AntoineAndre/alpha_dre/docs/renders/alpha_dre_top_view2.png

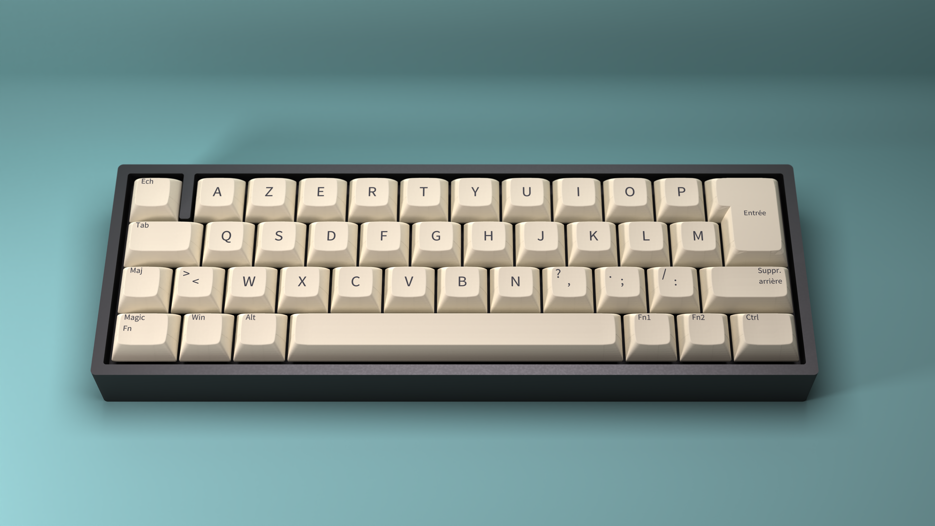
docs/renders/alpha_dre_top_view2.png
