AntoineAndre/alpha_dre/case/Rev2/solidworks_project/switch_plate.SLDPRT

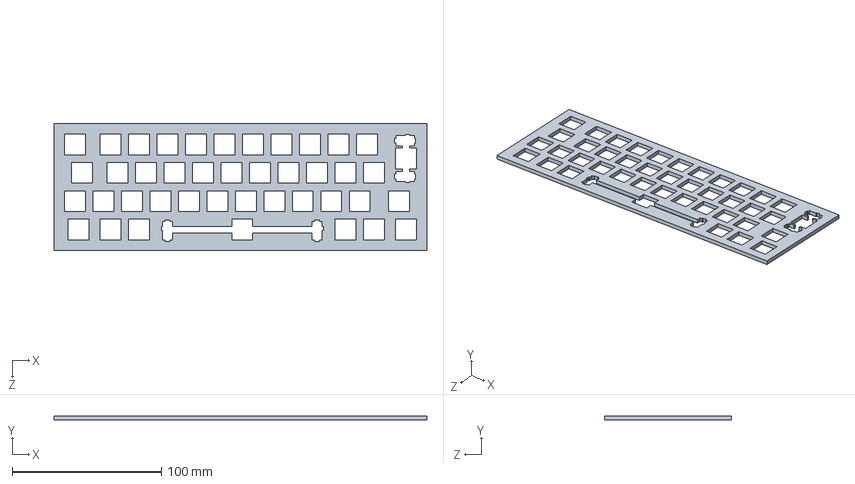
[picture p30: CAD file, 2021-06-06]
case/Rev2/solidworks_project/switch_plate.SLDPRT
249.6 x 3.00 x 85.2 mm
