AntoineAndre/alpha_dre/case/Acrylic_stack/Acrylic_files/case_foot_line.dxf

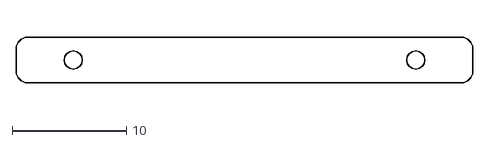
[picture p31: CAD file, 2021-04-18]
case/Acrylic_stack/Acrylic_files/case_foot_line.dxf
40.0 x 4.00
