AntoineAndre/alpha_dre/case/Acrylic_stack/STL/plate.stl

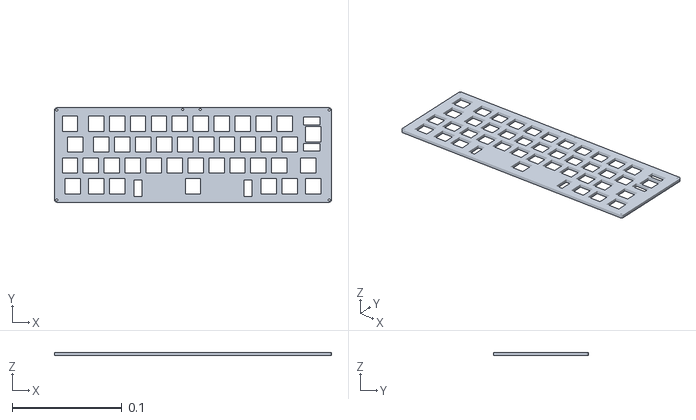
[picture p32: CAD file, 2021-04-17]
case/Acrylic_stack/STL/plate.stl
0.252 x 0.086 x 0.003
