AntoineAndre/alpha_dre/case/Acrylic_stack/Acrylic_files/case_bottom_line.dxf

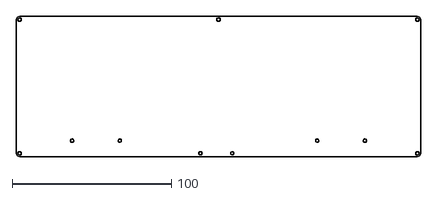
[picture p34: CAD file, 2021-04-18]
case/Acrylic_stack/Acrylic_files/case_bottom_line.dxf
254.1 x 88.1
